joao-beirao/BGreen/Circuitos/PAP_Circuito_Print.png

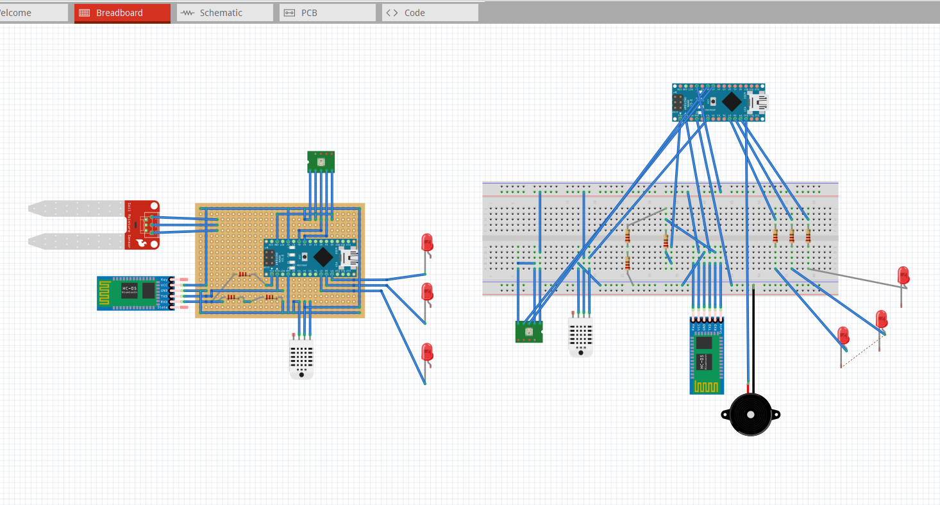
Circuitos/PAP_Circuito_Print.png
